jjg/rain-psp/docs/lcd_dimensions.jpg

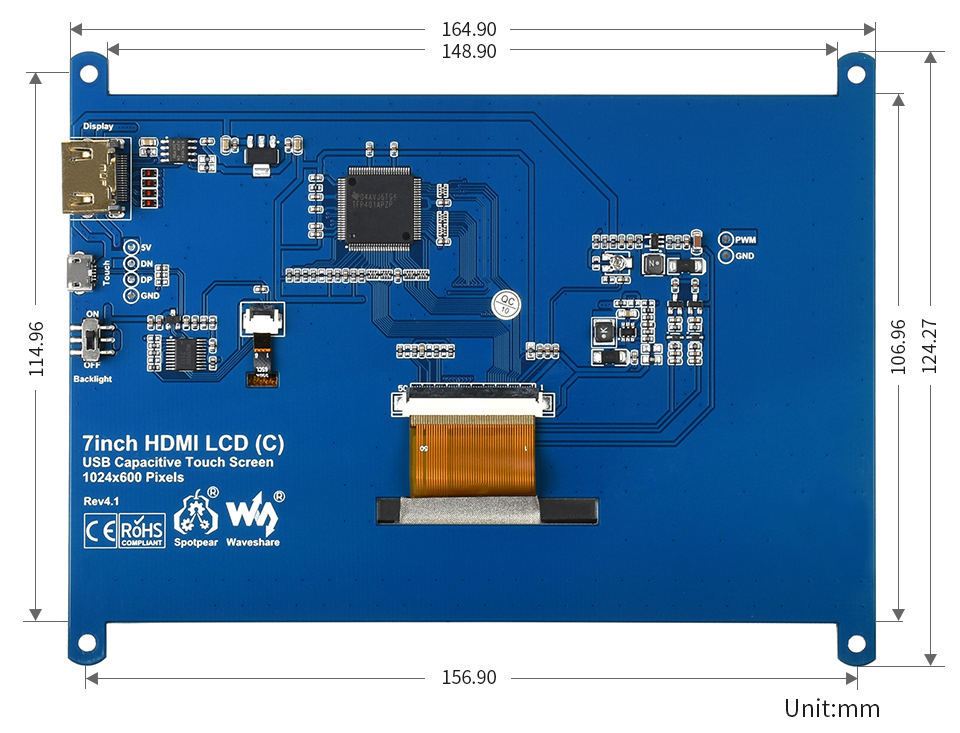
docs/lcd_dimensions.jpg
