jjg/rain-psp/docs/valentine.jpg

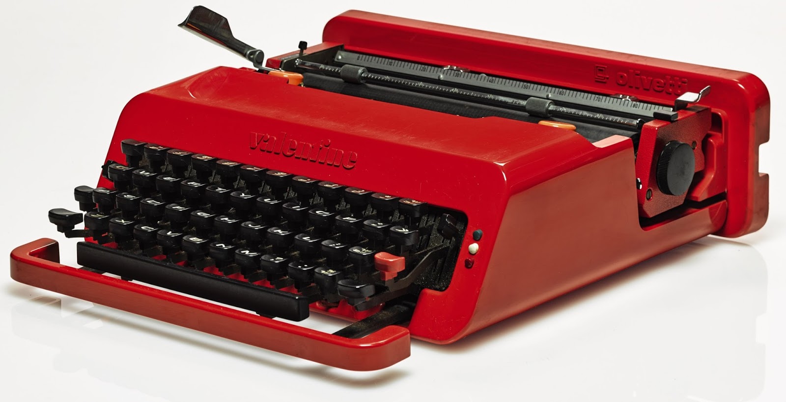
docs/valentine.jpg
