jjg/rain-psp/images/cvent.png

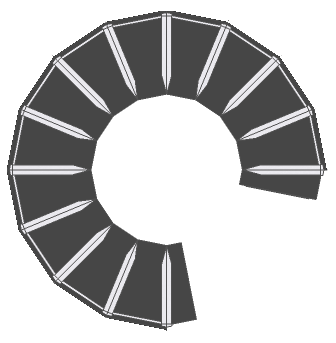
images/cvent.png
