jjg/rain-psp/hardware/models/case_bottom.stl

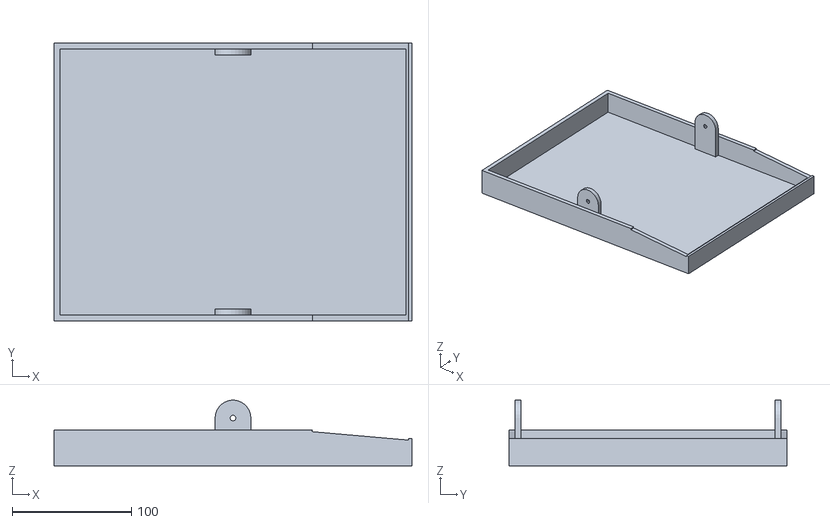
[picture p29: CAD file, 2021-10-07]
hardware/models/case_bottom.stl
300.0 x 233.0 x 54.9
