jjg/rain-psp/hardware/models/keys01.stl

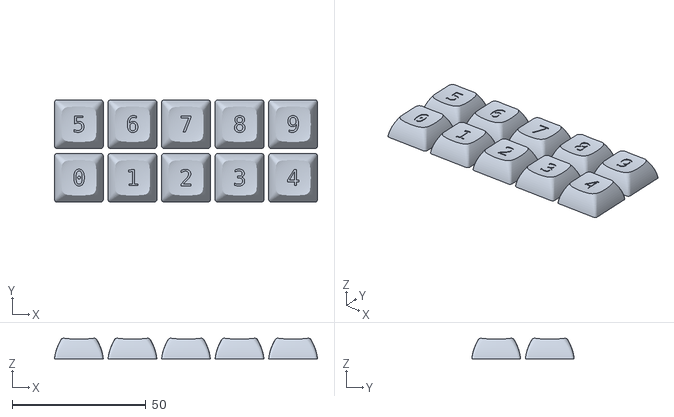
[picture p30: CAD file, 2021-10-06]
hardware/models/keys01.stl
98.2 x 38.2 x 7.67
