jjg/rain-psp/hardware/models/case_top.stl

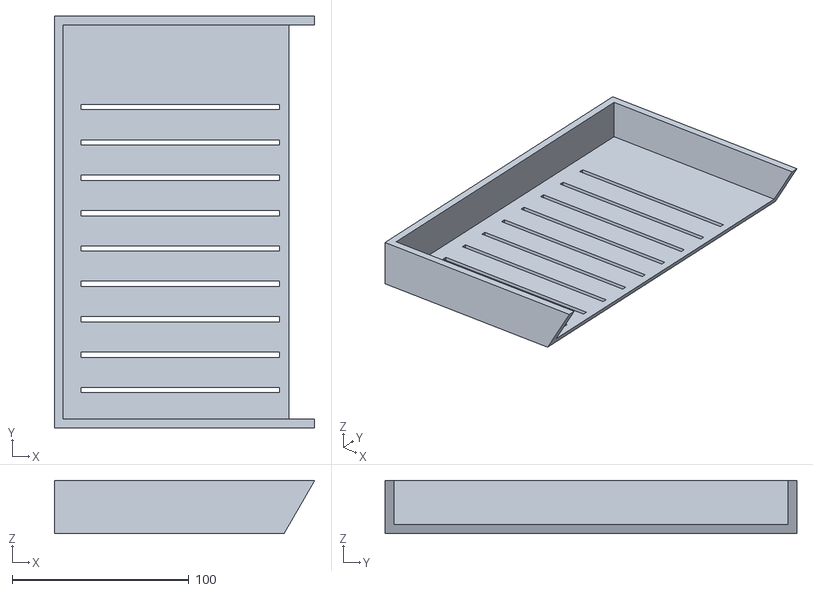
[picture p31: CAD file, 2021-10-03]
hardware/models/case_top.stl
147.3 x 233.0 x 30.0
