jjg/rain-psp/hardware/models/thumbscrew1.stl

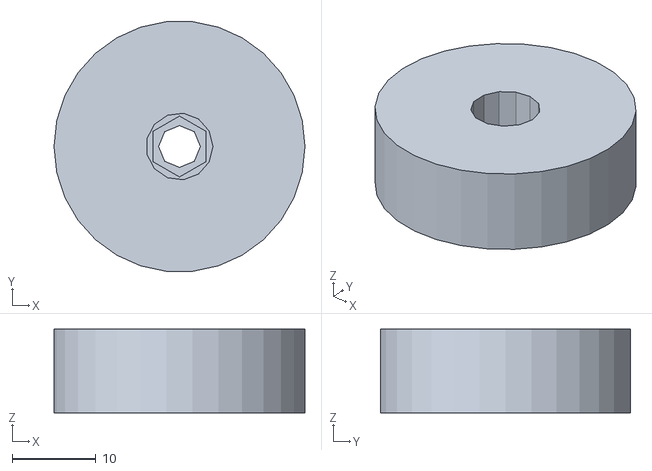
[picture p32: CAD file, 2021-11-16]
hardware/models/thumbscrew1.stl
30.0 x 29.8 x 10.0
