jjg/rain-psp/hardware/models/modules/pinea64.scad

module PINEA64(){
    /*
    Raw measurements:
    128x80x19
    */
    
    cube([135,80,19]);
}
