jjg/rain-psp/hardware/models/modules/fan.scad

module Fan(){
    cube([40,20,40]);
}
