jjg/rain-psp/hardware/models/modules/lcd.scad

module LCD(){
    
    /*
    eBay 1024x600 DSI LCD
    
    192x110x???
    */
    
    cube([192,110,10]);
}

//LCD();
