jjg/rain-psp/images/assembly_back_screenshot.png

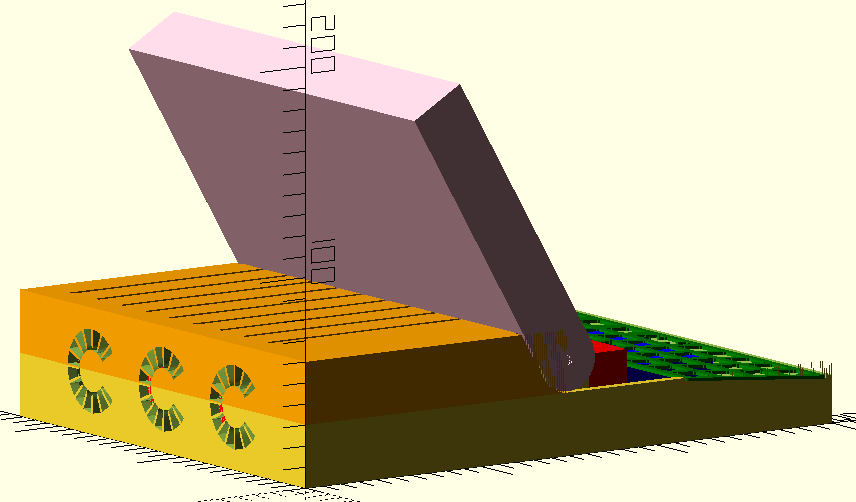
images/assembly_back_screenshot.png
